Universumgames/knock-knock-esp32/documentation/assets/piezo_knocks/piezo_knock_wave_1.jpeg

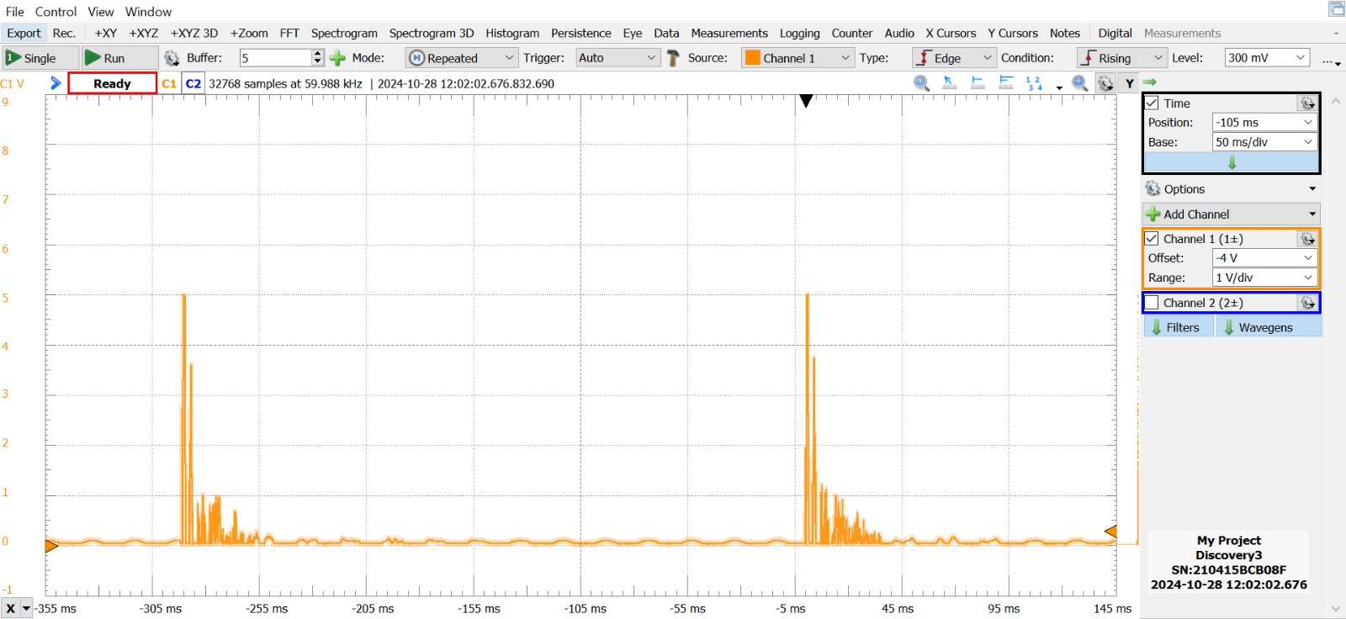
documentation/assets/piezo_knocks/piezo_knock_wave_1.jpeg
