Universumgames/knock-knock-esp32/documentation/assets/piezo_knocks/piezo_knock_wave_6.jpeg

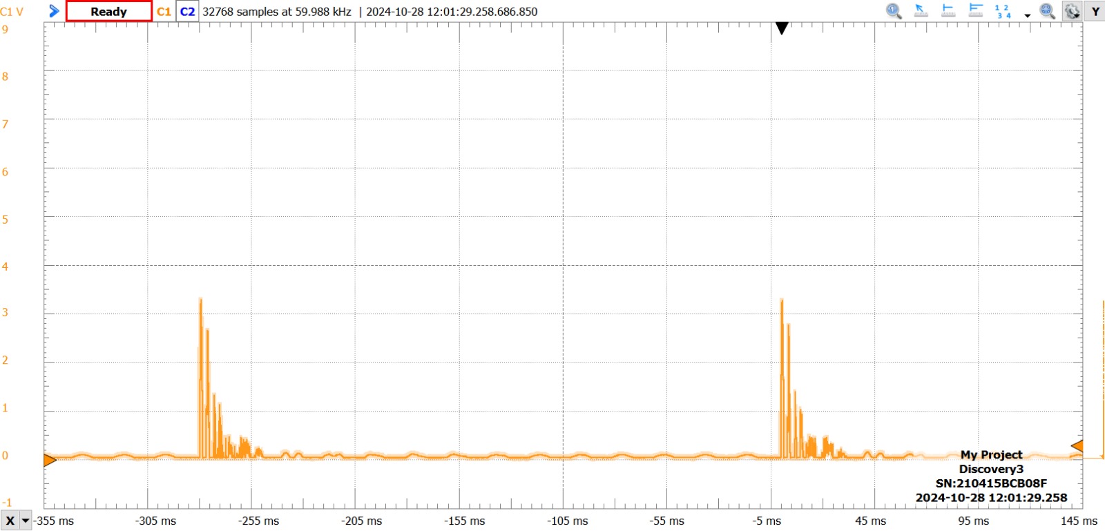
documentation/assets/piezo_knocks/piezo_knock_wave_6.jpeg
