Universumgames/knock-knock-esp32/documentation/assets/ws2812_spi_bit_encode.jpeg

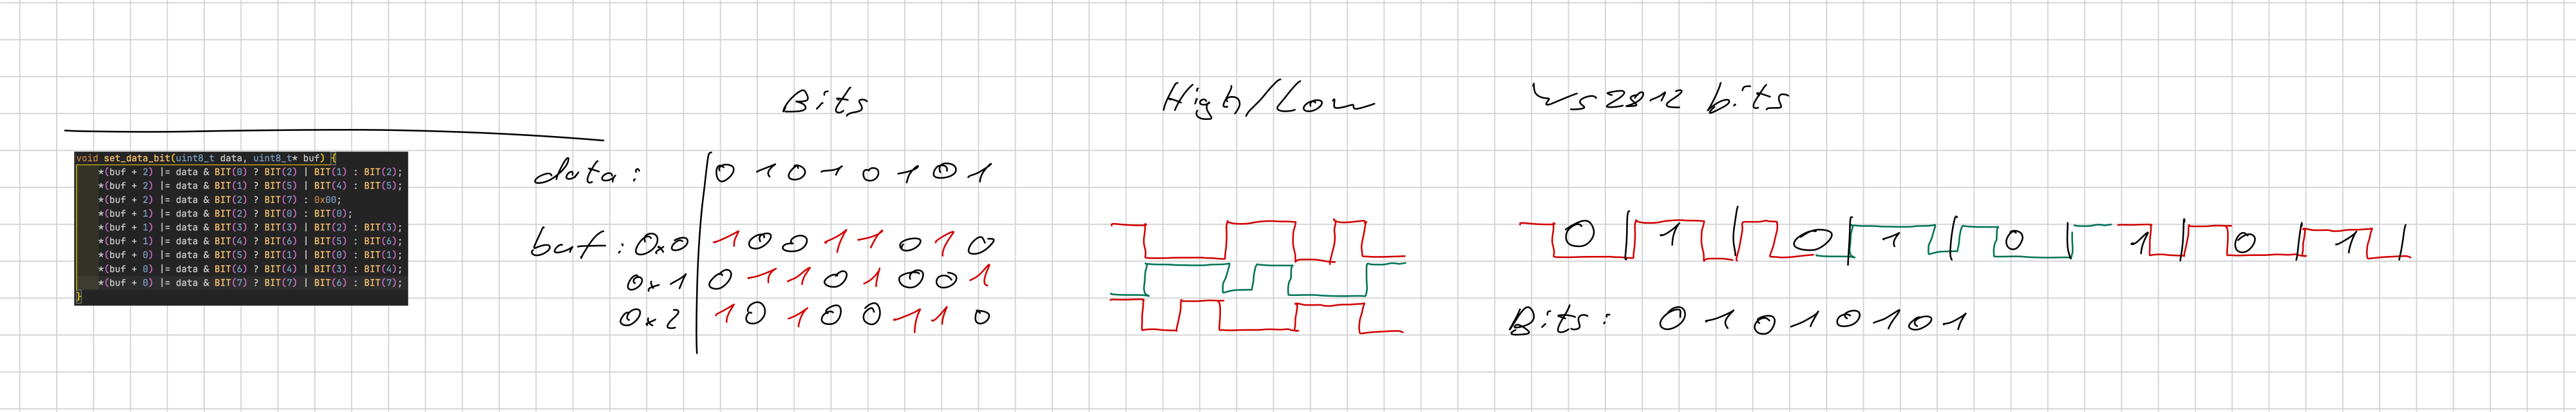
documentation/assets/ws2812_spi_bit_encode.jpeg
