Universumgames/knock-knock-esp32/utils/raw.png

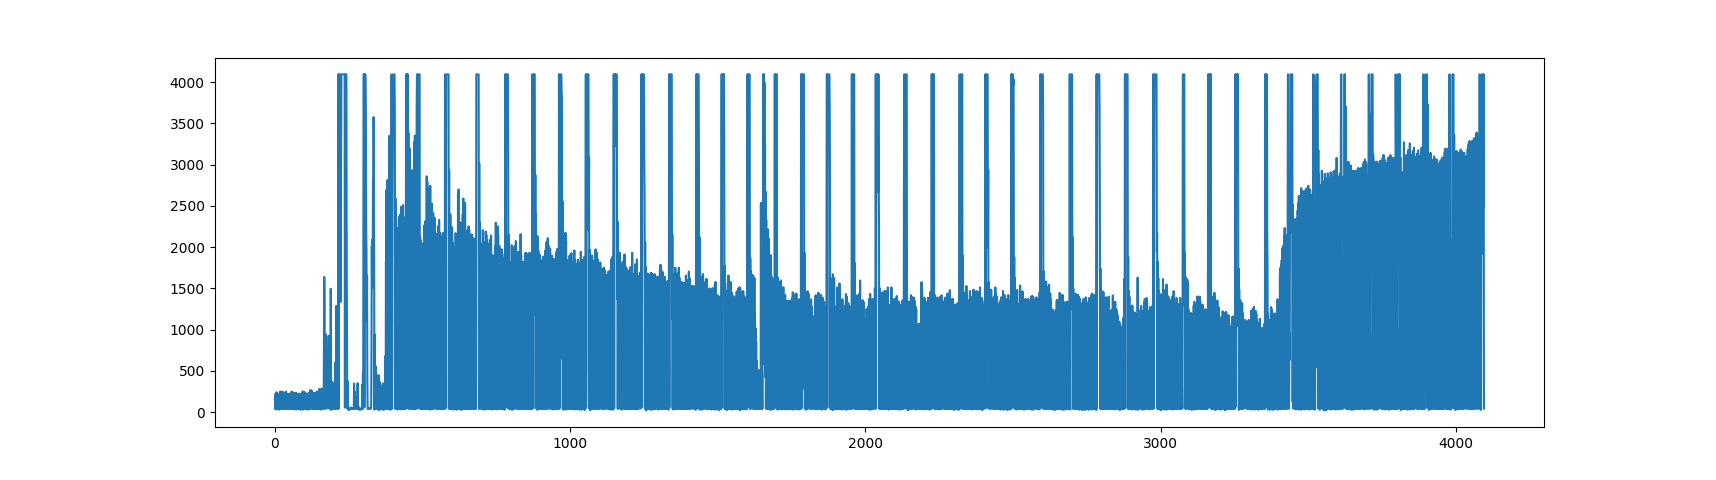
utils/raw.png
