Universumgames/knock-knock-esp32/utils/zoomed_in.png

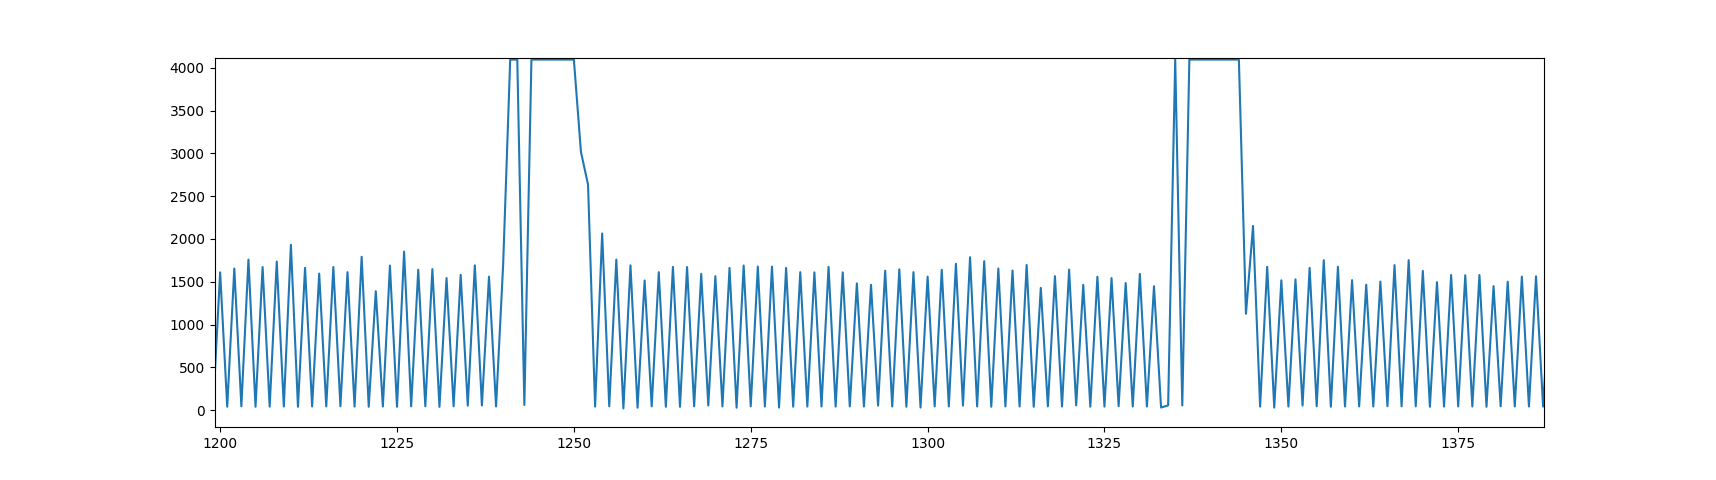
utils/zoomed_in.png
