Universumgames/knock-knock-esp32/testate/jovan_01/src/Serial.c

#include "Serial.h"

void initSerial(){
    setvbuf(stdin, NULL, _IONBF, 0);
    setvbuf(stdout, NULL, _IONBF, 0);
    ESP_ERROR_CHECK(uart_driver_install(CONFIG_ESP_CONSOLE_UART_NUM, 256, 0, 0, NULL, 0));
    esp_vfs_dev_uart_use_driver(CONFIG_ESP_CONSOLE_UART_NUM);
    esp_vfs_dev_uart_port_set_rx_line_endings(CONFIG_ESP_CONSOLE_UART_NUM, ESP_LINE_ENDINGS_CR);
    esp_vfs_dev_uart_port_set_tx_line_endings(CONFIG_ESP_CONSOLE_UART_NUM, ESP_LINE_ENDINGS_CRLF);
}
